wisdom-km/chroma-badge/hardware/enclosure/output/enclosure_side.png

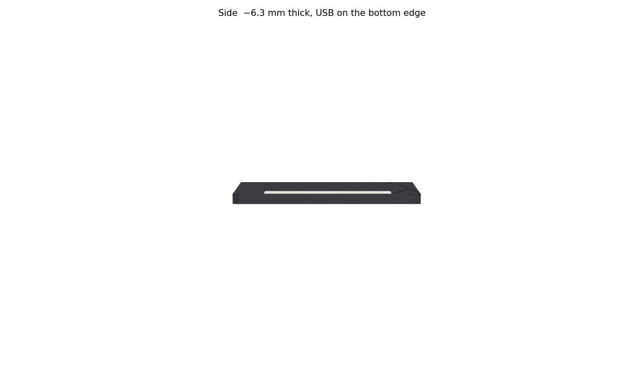
hardware/enclosure/output/enclosure_side.png
