wisdom-km/chroma-badge/hardware/pcb/output/j1_back_close.png

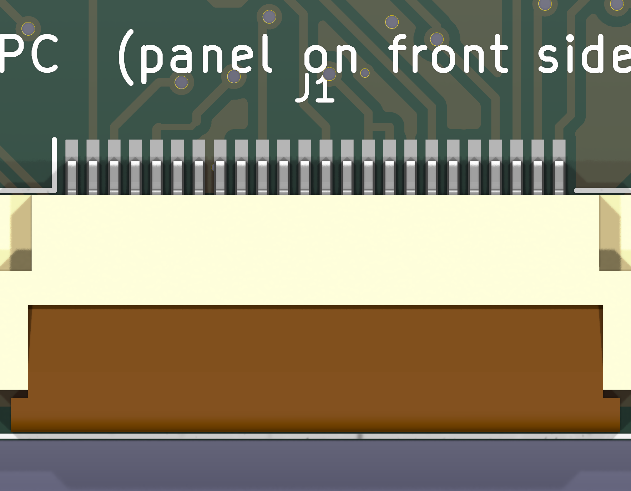
hardware/pcb/output/j1_back_close.png
