wisdom-km/chroma-badge/hardware/pcb/output/j1_from_slot.png

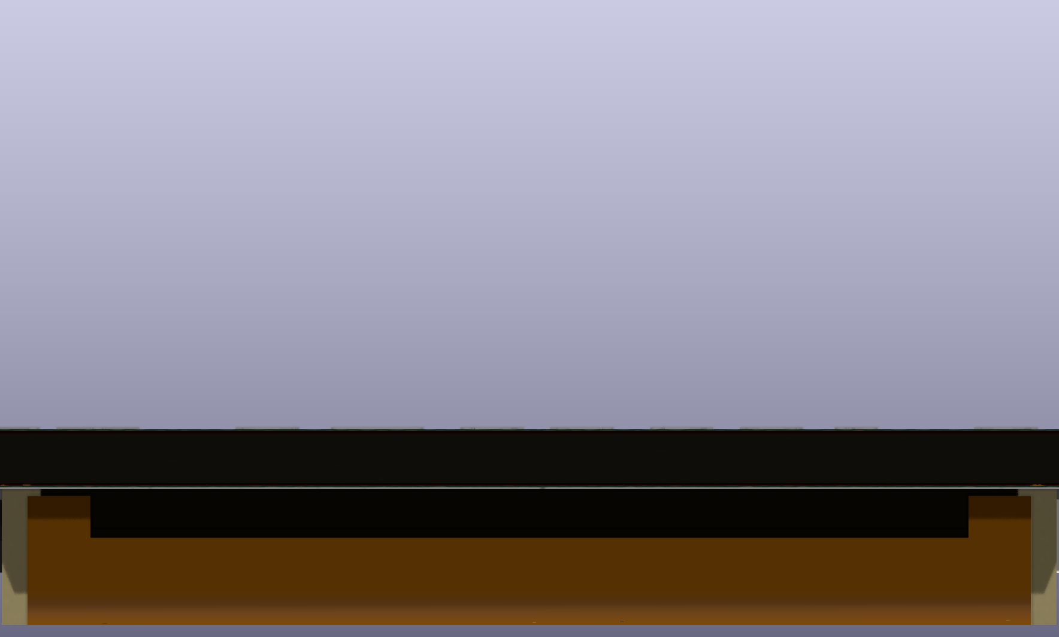
hardware/pcb/output/j1_from_slot.png
