wisdom-km/chroma-badge/hardware/pcb/output/j1_iso.png

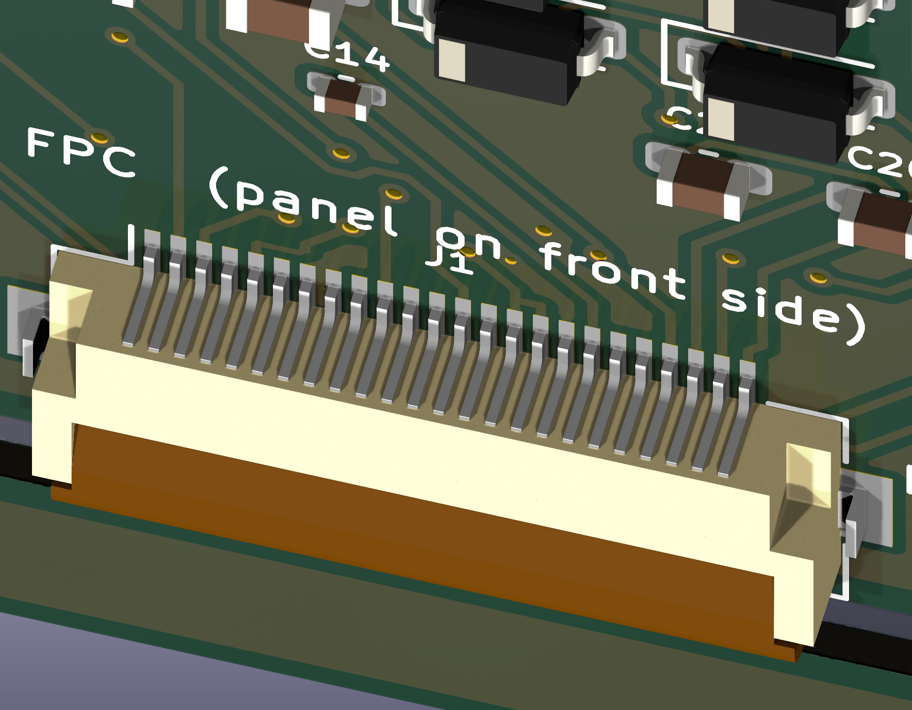
hardware/pcb/output/j1_iso.png
