wisdom-km/chroma-badge/hardware/pcb/output/nfc_coil_close.png

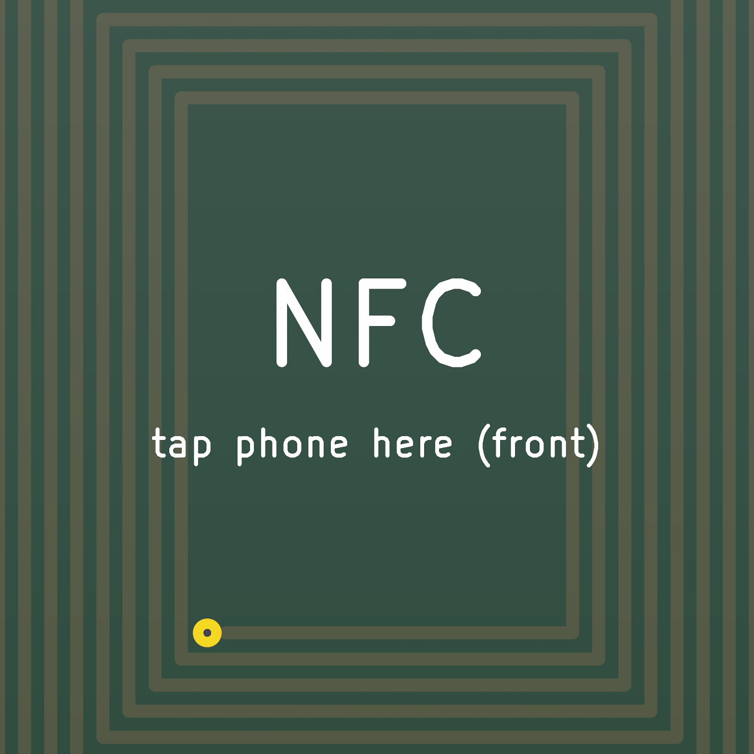
hardware/pcb/output/nfc_coil_close.png
