wisdom-km/chroma-badge/hardware/pcb/output/render_front.png

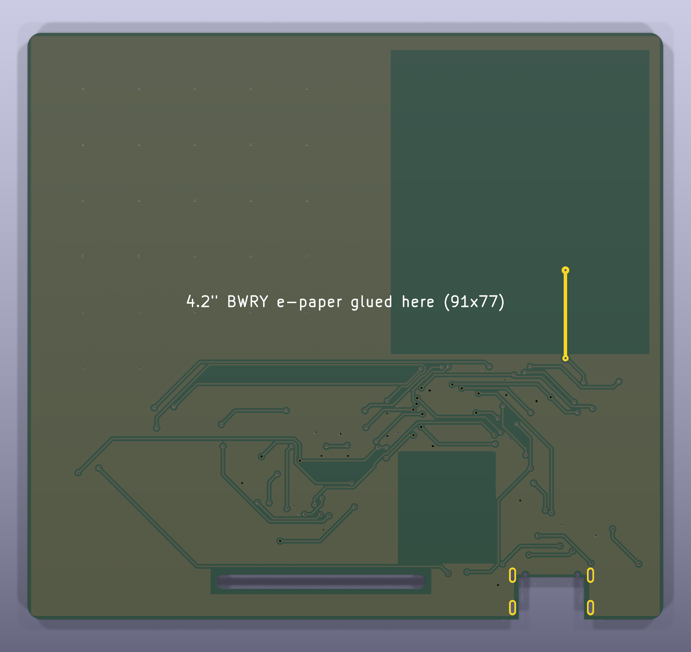
hardware/pcb/output/render_front.png
