wisdom-km/chroma-badge/hardware/pcb/output/silk_buttons.png

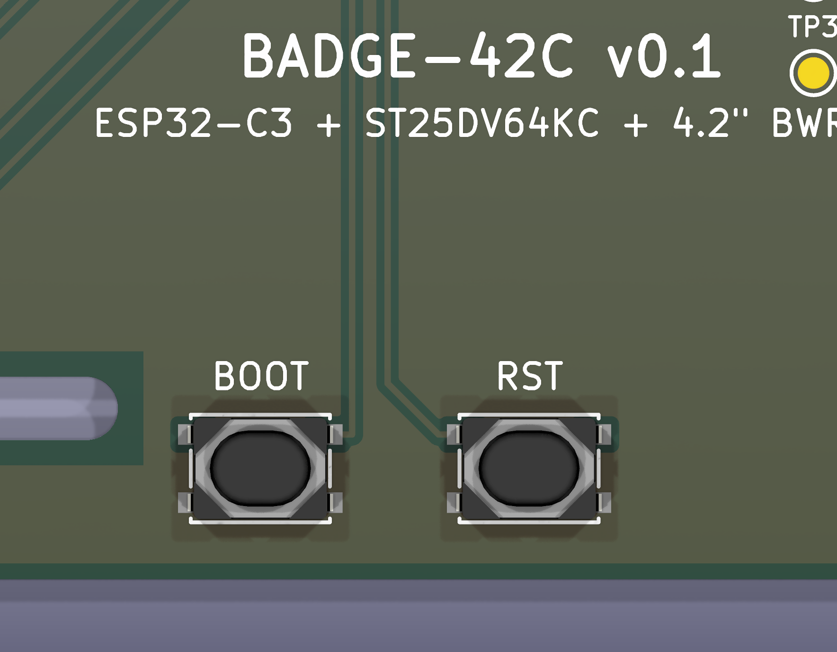
hardware/pcb/output/silk_buttons.png
