wisdom-km/chroma-badge/firmware/include/epd.h

#pragma once

#include <cstdint>

/* GDEM042F86 / SSD2683ZA, 400x300, 2 bit/pixel BWRY.
 * Init sequence: official spec 2026-06-17 section 10.2 (LUT from OTP). */

namespace epd {

constexpr int WIDTH = 400;
constexpr int HEIGHT = 300;
constexpr int FRAME_BYTES = WIDTH * HEIGHT / 4;  // 2 bpp packed, 4 px/byte

enum class Color : uint8_t {
    Black  = 0b00,
    White  = 0b01,
    Yellow = 0b10,
    Red    = 0b11,
};

void begin();
bool power_on();   // false if BUSY never cycles; still call power_off()
bool power_off();  // always cuts EPD_PWR_EN; false if BUSY timed out
bool refresh_solid(Color color);  // OTP full update, then panel deep-sleep + rail off
extern const char *last_fail;    // last wait stage name, or empty

}  // namespace epd
